westonb/leery-lisn/doc/measurements/l_dm.csv

Machine Module SVA1032X Plus
Trace Name | Trace A
Meas Type | S21
Start Frequency | +1.000000000E+05
Stop Frequency | +5.000000000E+07
Format | Log Mag
IFBW | 1.000000e+04
Trace Data
Frequency | Formatted Data
1.000000e+05 | -1.555599e+01
1.665333e+05 | -1.427402e+01
2.330667e+05 | -1.371709e+01
2.996000e+05 | -1.348805e+01
3.661333e+05 | -1.340804e+01
4.326667e+05 | -1.332417e+01
4.992000e+05 | -1.327528e+01
5.657333e+05 | -1.323404e+01
6.322667e+05 | -1.322950e+01
6.988000e+05 | -1.321322e+01
7.653333e+05 | -1.320828e+01
8.318667e+05 | -1.320018e+01
8.984000e+05 | -1.318644e+01
9.649333e+05 | -1.317471e+01
1.031467e+06 | -1.316945e+01
1.098000e+06 | -1.315539e+01
1.164533e+06 | -1.316707e+01
1.231067e+06 | -1.316281e+01
1.297600e+06 | -1.315865e+01
1.364133e+06 | -1.316030e+01
1.430667e+06 | -1.315379e+01
1.497200e+06 | -1.315020e+01
1.563733e+06 | -1.315572e+01
1.630267e+06 | -1.314670e+01
1.696800e+06 | -1.314785e+01
1.763333e+06 | -1.314277e+01
1.829867e+06 | -1.313157e+01
1.896400e+06 | -1.315249e+01
1.962933e+06 | -1.313592e+01
2.029467e+06 | -1.316843e+01
2.096000e+06 | -1.314799e+01
2.162533e+06 | -1.315370e+01
2.229067e+06 | -1.315254e+01
2.295600e+06 | -1.314843e+01
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
