westonb/leery-lisn/doc/measurements/l_impedance.csv

Machine Module SVA1032X Plus
Trace Name | Trace A
Meas Type | S11
Start Frequency | +1.000000000E+05
Stop Frequency | +5.000000000E+07
Format | Smith | R+jX
IFBW | 1.000000e+04
Trace Data
Frequency | Formatted Data
1.000000e+05 | 1.983267e+01 | 2.081480e+01 | 3.312778e-05 | H
1.665333e+05 | 3.016127e+01 | 2.162673e+01 | 2.066854e-05 | H
2.330667e+05 | 3.673388e+01 | 1.952008e+01 | 1.332974e-05 | H
2.996000e+05 | 4.061955e+01 | 1.763570e+01 | 9.368518e-06 | H
3.661333e+05 | 4.317451e+01 | 1.526229e+01 | 6.634383e-06 | H
4.326667e+05 | 4.454842e+01 | 1.376586e+01 | 5.063722e-06 | H
4.992000e+05 | 4.563501e+01 | 1.260113e+01 | 4.017491e-06 | H
5.657333e+05 | 4.642926e+01 | 1.130018e+01 | 3.179022e-06 | H
6.322667e+05 | 4.701291e+01 | 1.031044e+01 | 2.595357e-06 | H
6.988000e+05 | 4.756042e+01 | 9.417723e+00 | 2.144930e-06 | H
7.653333e+05 | 4.783138e+01 | 8.984849e+00 | 1.868445e-06 | H
8.318667e+05 | 4.805029e+01 | 8.207336e+00 | 1.570249e-06 | H
8.984000e+05 | 4.831256e+01 | 7.678782e+00 | 1.360325e-06 | H
9.649333e+05 | 4.840814e+01 | 7.745873e+00 | 1.277595e-06 | H
1.031467e+06 | 4.858470e+01 | 7.184814e+00 | 1.108614e-06 | H
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
