westonb/leery-lisn/doc/measurements/n_dm.csv

Machine Module SVA1032X Plus
Trace Name | Trace A
Meas Type | S21
Start Frequency | +1.000000000E+05
Stop Frequency | +5.000000000E+07
Format | Log Mag
IFBW | 1.000000e+04
Trace Data
Frequency | Formatted Data
1.000000e+05 | -1.575369e+01
1.665333e+05 | -1.420895e+01
2.330667e+05 | -1.376292e+01
2.996000e+05 | -1.353528e+01
3.661333e+05 | -1.343795e+01
4.326667e+05 | -1.333094e+01
4.992000e+05 | -1.330690e+01
5.657333e+05 | -1.324371e+01
6.322667e+05 | -1.323627e+01
6.988000e+05 | -1.321268e+01
7.653333e+05 | -1.319691e+01
8.318667e+05 | -1.316570e+01
8.984000e+05 | -1.318374e+01
9.649333e+05 | -1.318404e+01
1.031467e+06 | -1.316094e+01
1.098000e+06 | -1.316725e+01
1.164533e+06 | -1.315436e+01
1.231067e+06 | -1.316845e+01
1.297600e+06 | -1.315573e+01
1.364133e+06 | -1.315205e+01
1.430667e+06 | -1.315982e+01
1.497200e+06 | -1.315662e+01
1.563733e+06 | -1.315701e+01
1.630267e+06 | -1.314972e+01
1.696800e+06 | -1.314522e+01
1.763333e+06 | -1.315032e+01
1.829867e+06 | -1.314963e+01
1.896400e+06 | -1.315566e+01
1.962933e+06 | -1.315658e+01
2.029467e+06 | -1.314879e+01
2.096000e+06 | -1.315124e+01
2.162533e+06 | -1.315320e+01
2.229067e+06 | -1.315675e+01
2.295600e+06 | -1.315728e+01
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
