westonb/leery-lisn/doc/measurements/n_impedance.csv

Machine Module SVA1032X Plus
Trace Name | Trace A
Meas Type | S11
Start Frequency | +1.000000000E+05
Stop Frequency | +5.000000000E+07
Format | Smith | R+jX
IFBW | 1.000000e+04
Trace Data
Frequency | Formatted Data
1.000000e+05 | 2.002167e+01 | 2.148455e+01 | 3.419373e-05 | H
1.665333e+05 | 3.059076e+01 | 2.177786e+01 | 2.081298e-05 | H
2.330667e+05 | 3.725801e+01 | 1.942388e+01 | 1.326404e-05 | H
2.996000e+05 | 4.090846e+01 | 1.740873e+01 | 9.247950e-06 | H
3.661333e+05 | 4.330336e+01 | 1.505560e+01 | 6.544538e-06 | H
4.326667e+05 | 4.479021e+01 | 1.345433e+01 | 4.949128e-06 | H
4.992000e+05 | 4.590286e+01 | 1.219344e+01 | 3.887512e-06 | H
5.657333e+05 | 4.657150e+01 | 1.088872e+01 | 3.063268e-06 | H
6.322667e+05 | 4.716941e+01 | 9.807193e+00 | 2.468679e-06 | H
6.988000e+05 | 4.759676e+01 | 9.197142e+00 | 2.094692e-06 | H
7.653333e+05 | 4.784035e+01 | 8.649573e+00 | 1.798723e-06 | H
8.318667e+05 | 4.810947e+01 | 7.746967e+00 | 1.482170e-06 | H
8.984000e+05 | 4.828493e+01 | 7.521292e+00 | 1.332425e-06 | H
9.649333e+05 | 4.841949e+01 | 7.165124e+00 | 1.181807e-06 | H
1.031467e+06 | 4.858674e+01 | 6.710001e+00 | 1.035351e-06 | H
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
