westonb/leery-lisn/sim/limiter.asc

C1: cap; 0.47µ
C2: cap; 0.47µ
C3: cap; 0.1µ
C4: cap; 4p
D1: diode; 1N4148
D2: diode; 1N4148
D3: diode; 1N4148
D4: diode; 1N4148
L1: ind; 1m
L2: ind; 5µ
R1: res; 620
R2: res; 560
R3: res; 18
R4: res; 430
R5: res; 430
R6: res; 220
R7: res; 30
R8: res; 240
R9: res; 270
R10: res; 12
R11: res; 910
R12: res; 820
R13: res; 50
R14: res; 0.2
R15: res; 40
V1: voltage; PULSE(0 270 10u 10n 10n 1m 2m); AC 1
Named nets: 0
.tran 0.5m
